thiagolr/keytita/cad/KeyTita_Printer_Connector.stl

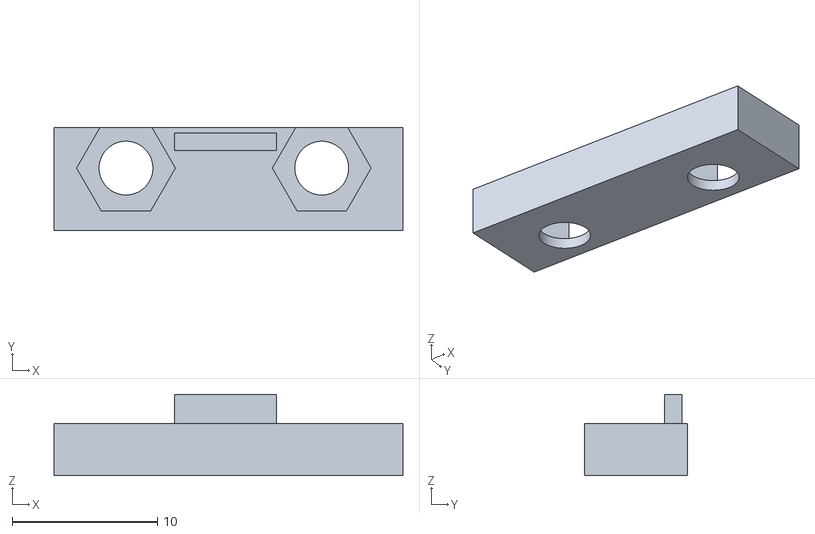
[picture p27: CAD file, 2020-07-13]
cad/KeyTita_Printer_Connector.stl
24.0 x 7.10 x 5.60
