thiagolr/keytita/cad/KeyTita_Printer_C0_Front.stl

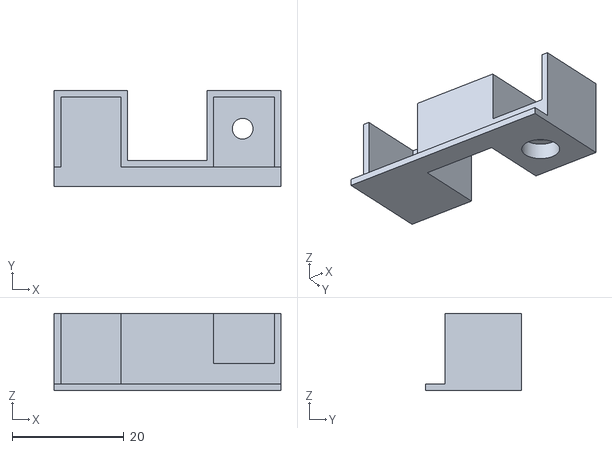
[picture p28: CAD file, 2020-07-13]
cad/KeyTita_Printer_C0_Front.stl
40.6 x 17.2 x 13.8
