thiagolr/keytita/cad/KeyTita_Printer_C2C3C4C5C6_Front.stl

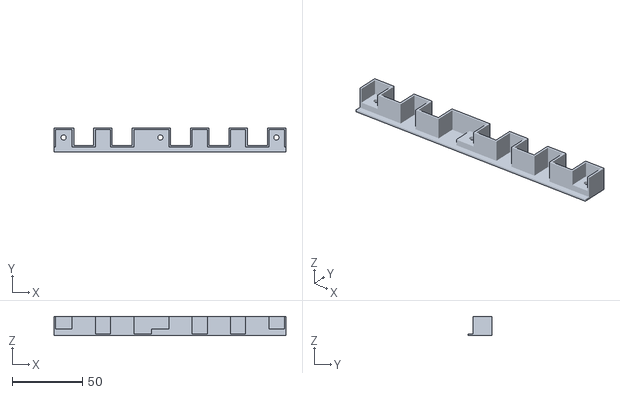
[picture p29: CAD file, 2020-07-13]
cad/KeyTita_Printer_C2C3C4C5C6_Front.stl
165.0 x 17.2 x 13.8
