thiagolr/keytita/cad/KeyTita_Printer_C0_Back.stl

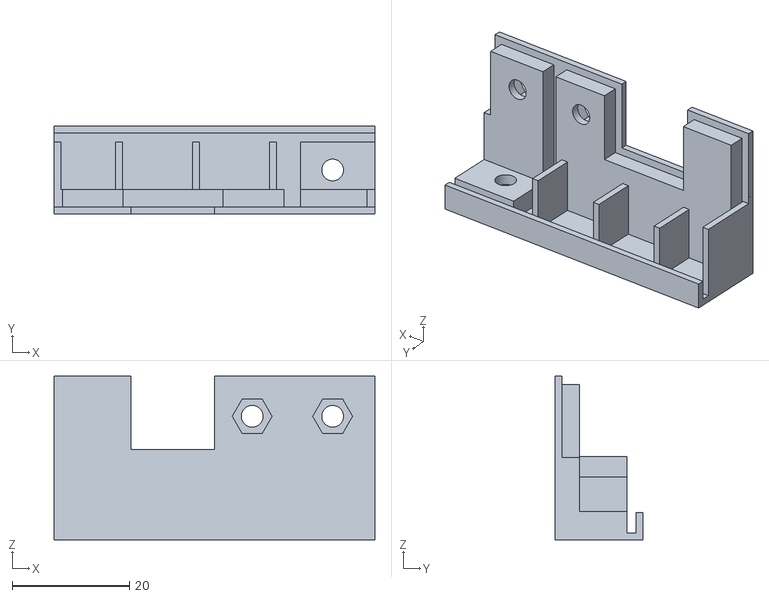
[picture p30: CAD file, 2020-07-13]
cad/KeyTita_Printer_C0_Back.stl
54.7 x 15.0 x 27.9
