thiagolr/keytita/cad/KeyTita_Demo_Exploded.stl

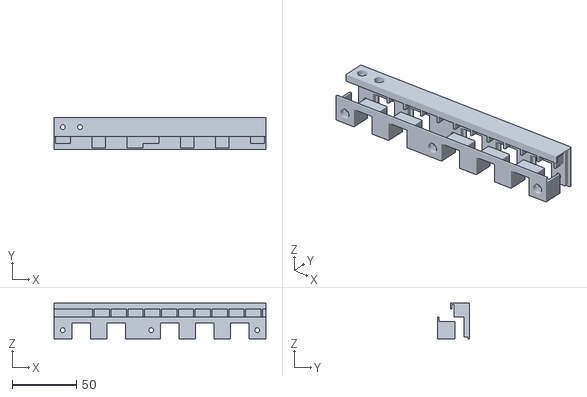
[picture p31: CAD file, 2020-07-13]
cad/KeyTita_Demo_Exploded.stl
165.0 x 25.0 x 27.9
